gerb-ster/Steiner-VCF/images/IMG_3991.jpeg

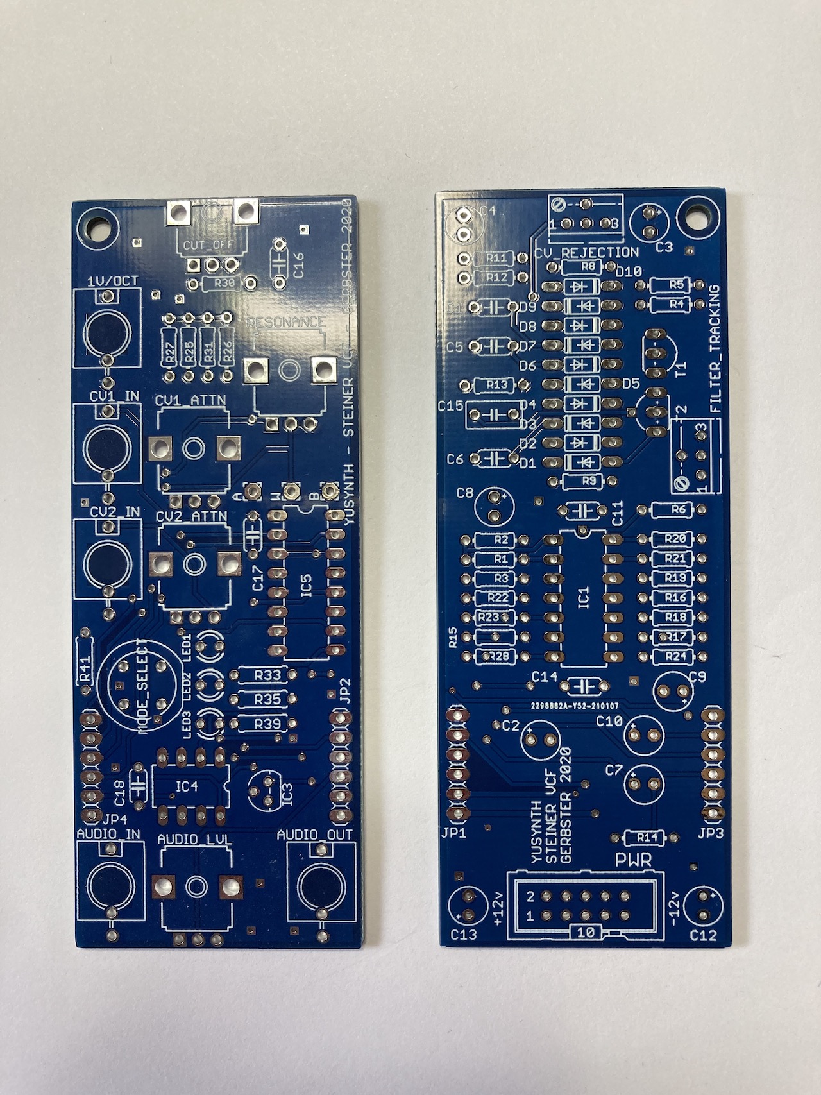
images/IMG_3991.jpeg
