gerb-ster/Steiner-VCF/images/IMG_3999.jpeg

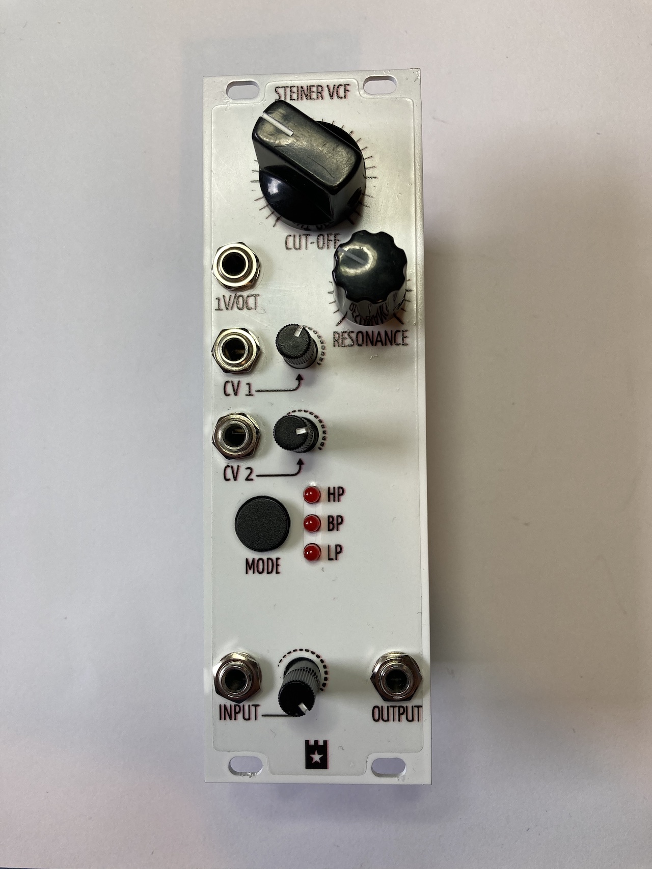
images/IMG_3999.jpeg
