gerb-ster/Steiner-VCF/images/IMG_4001.jpeg

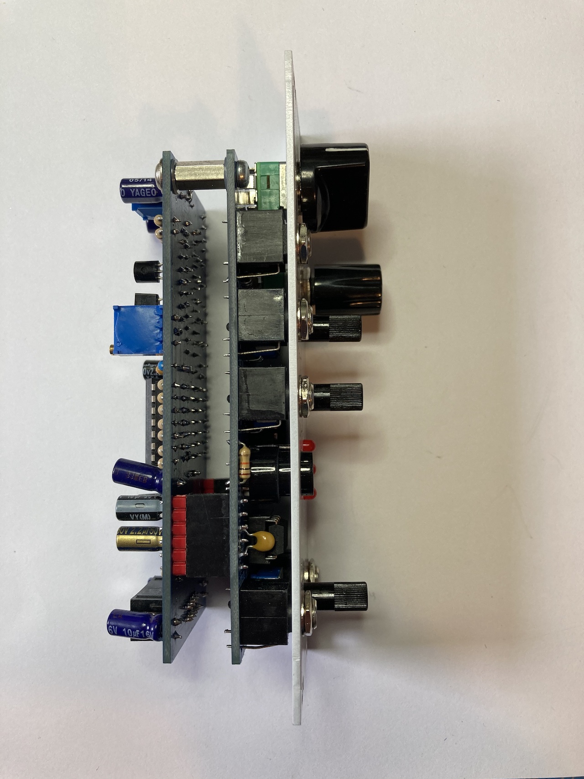
images/IMG_4001.jpeg
