gerb-ster/Steiner-VCF/images/IMG_4003.jpeg

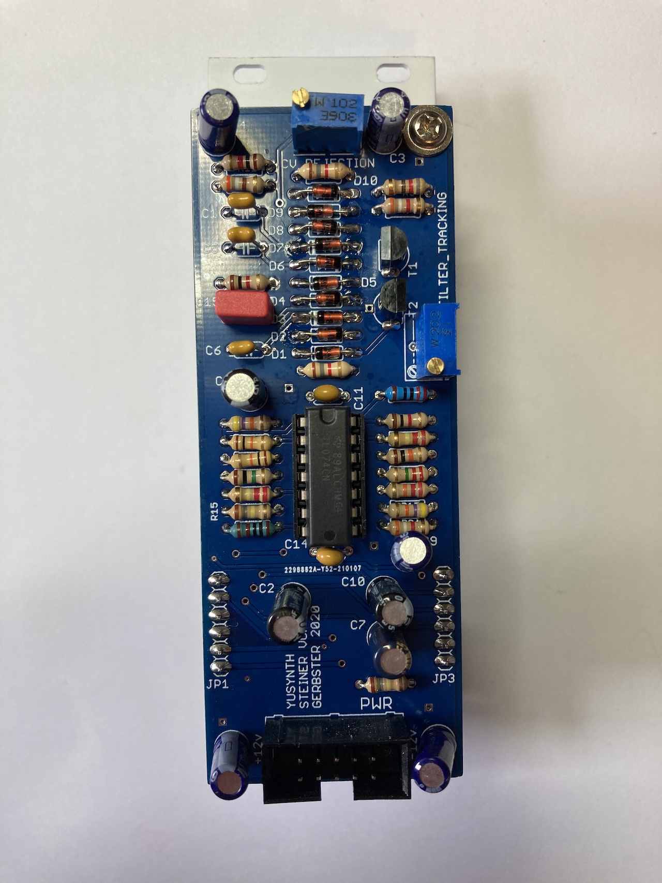
images/IMG_4003.jpeg
