gerb-ster/Steiner-VCF/images/IMG_4004.jpeg

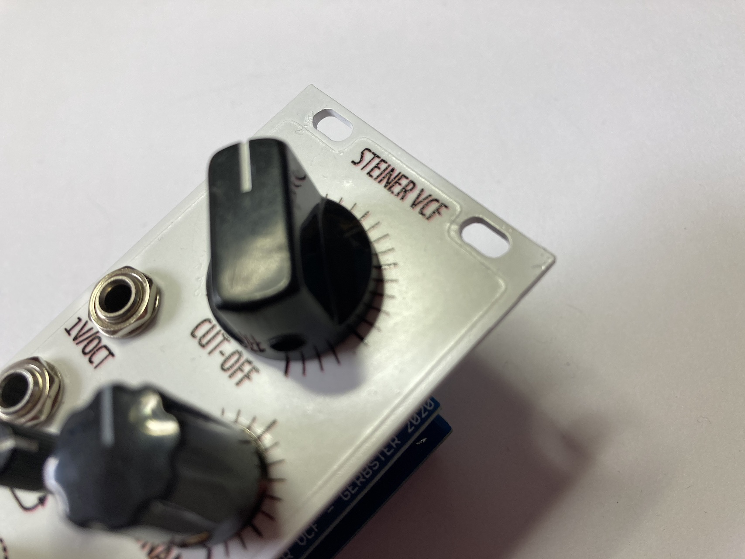
images/IMG_4004.jpeg
