gerb-ster/Steiner-VCF/images/IMG_4005.jpeg

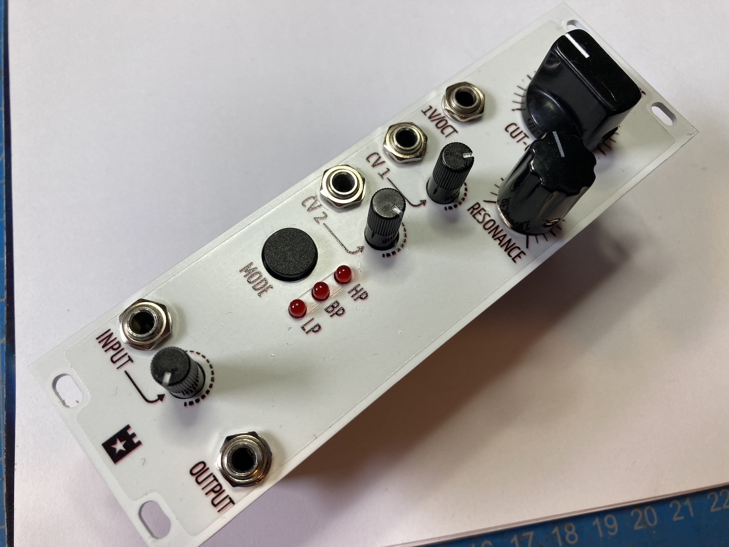
images/IMG_4005.jpeg
