gerb-ster/Steiner-VCF/images/IMG_4006.jpeg

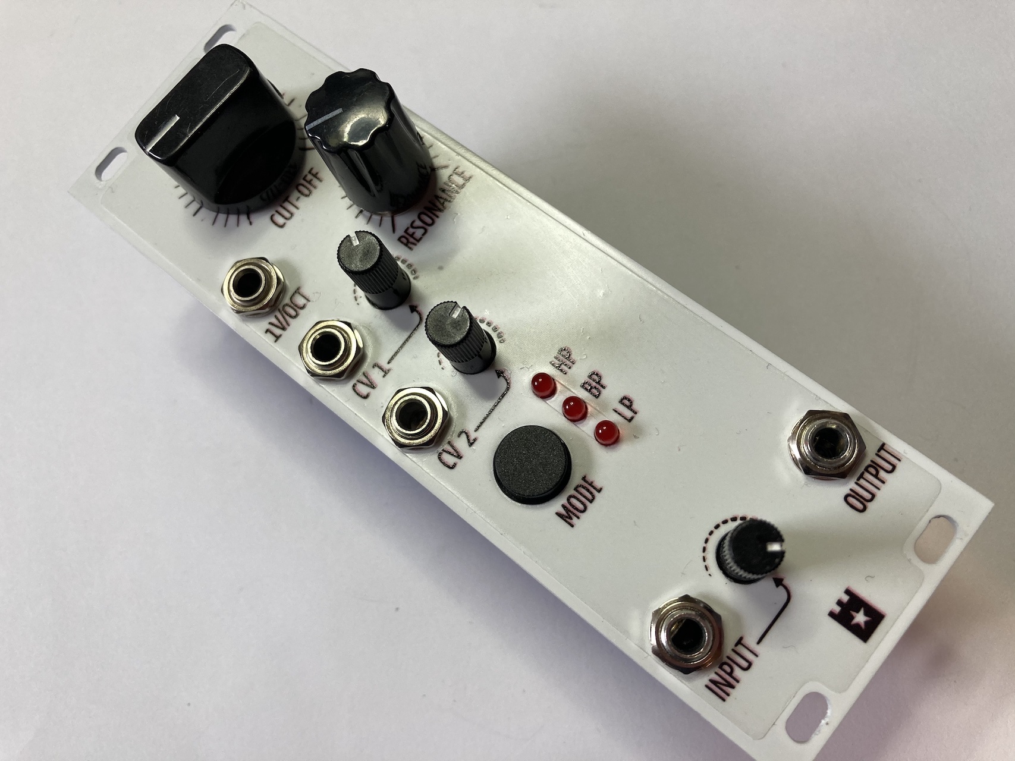
images/IMG_4006.jpeg
